MonsterMaze/Eprom_USB/soft_Win64_v2/src/ArduinoIO.h

/**
 * 
 * Eprom Programmer
 * 
 * Copyright (C) 2021-2023 Ciprian Stingu
 * ciprian stingu at gmail dot com
 * 
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
 */
//----------------------------------------------------------------------
#ifndef ARDUINO_IO_H
#define ARDUINO_IO_H
//----------------------------------------------------------------------
#include <QObject>
#include <QSerialPort>
#include <QElapsedTimer>
#include "structs.h"
//----------------------------------------------------------------------

class ArduinoIO : public QObject
{
    Q_OBJECT

private:
    const char *COMMAND_FLAG           = "@CMD";
    const char *COMMAND_SET_EPROM_TYPE = "@CMDTYPE%2d";
    const char *COMMAND_VOLTAGE_INFO   = "@CMDVINF";
    const char *COMMAND_READ_EPROM     = "@CMDREAD";
    const char *COMMAND_HW_TEST        = "@CMDTEST";
    const char *COMMAND_WRITE_EPROM    = "@CMDWRIT%5.2f%5.2f%2d";
    const char *RESPONSE_OK            = "@RSPOK  ";
    const char *RESPONSE_VOLTAGE_INFO  = "@RSPVINF";
    const char *RESPONSE_READ_EPROM    = "@RSPREAD";
    const char *RESPONSE_HW_TEST_ON    = "@RSPTEST ON";
    const char *RESPONSE_HW_TEST_OFF   = "@RSPTEST OFF";
    const char *RESPONSE_ERROR         = "@RSPERR ";
    const char *RESPONSE_WRITE_EPROM   = "@RSPWRIT";
    const char *RESPONSE_WRITE_BLOCK   = "@RSPBLCK";

    EPROM_TYPE selectedEpromType;
    QSerialPort *serialPort = nullptr;
    QByteArray readBuffer;
    QByteArray writeBuffer;
    int maxBufferSize;
    PRG_ALGO programmingAlghoritm;

    // === NUEVAS VARIABLES PARA EL MOTOR ASINCRÓNICO ===
    QByteArray m_incomingBuffer; // Acumulador centralizado de bytes del puerto
    enum EstadoOperacion { Idle, LeyendoVoltajes, LeyendoEprom, TesteandoHw, GrabandoEprom };
    EstadoOperacion m_estadoActual;
    int m_bloqueGrabacionActual;
    // NOTA: No agregues ninguna línea con BLOCK_SIZE acá, ya la lee de defines.h solo.
    // ==================================================

    void Send(const QByteArray &data);
    void ResetVariables(void);
    QString CleanErrorMessage(QByteArray errorMessage);
    void procesarLineaRecibida(const QByteArray &linea);

private slots:
    // El único slot real que escucha al puerto serial sin bloquear la app
    void onReadyRead(void);

    // Mantenemos estos slots por si la UI los invoca de forma directa
    void SelectEpromSlot(void);
    void ReadVoltageSlot(void);
    void ReadEpromSlot(void);
    void HarwareTestSlot(void);
    void WriteEpromSlot(void);

public:
    const char *HW_TEST_END = "Hardware test end.\n";

    ArduinoIO(QSerialPort *port);
    ~ArduinoIO();
    int GetEpromSize(void);
    QByteArray *GetReadBuffer(void);
    QByteArray *GetWriteBuffer(void);
    void SelectEprom(EPROM_TYPE type);
    void ReadVoltage(void);
    void ReadEprom(void);
    void HardwareTest(void);
    void WriteEprom(double vcc, double vpp, PRG_ALGO algo);

signals:
    // MANTENEMOS TODAS TUS SEÑALES ORIGINALES INTACTAS
    void SerialOperationStartSignal(void);
    void SerialOperationErrorSignal(const char *);
    void SerialOperationCompleteSignal(void);
    void VoltageUpdatedSignal(double, double);
    void ReadBlockSignal(int);
    void ReadCompleteSignal(void);
    void HardwareTestStepSignal(const char *);
    void ReadEpromDataSignal(int, int, uint8_t *);
    void WriteBlockSignal(int);
    void WriteCompleteSignal(bool, const char *);
};

//----------------------------------------------------------------------
#endif
